baidu/boteye_sensor/hardware/XP3/schematic&PCB PDF/schematic/XPIAC-C_1V3_SCH.pdf

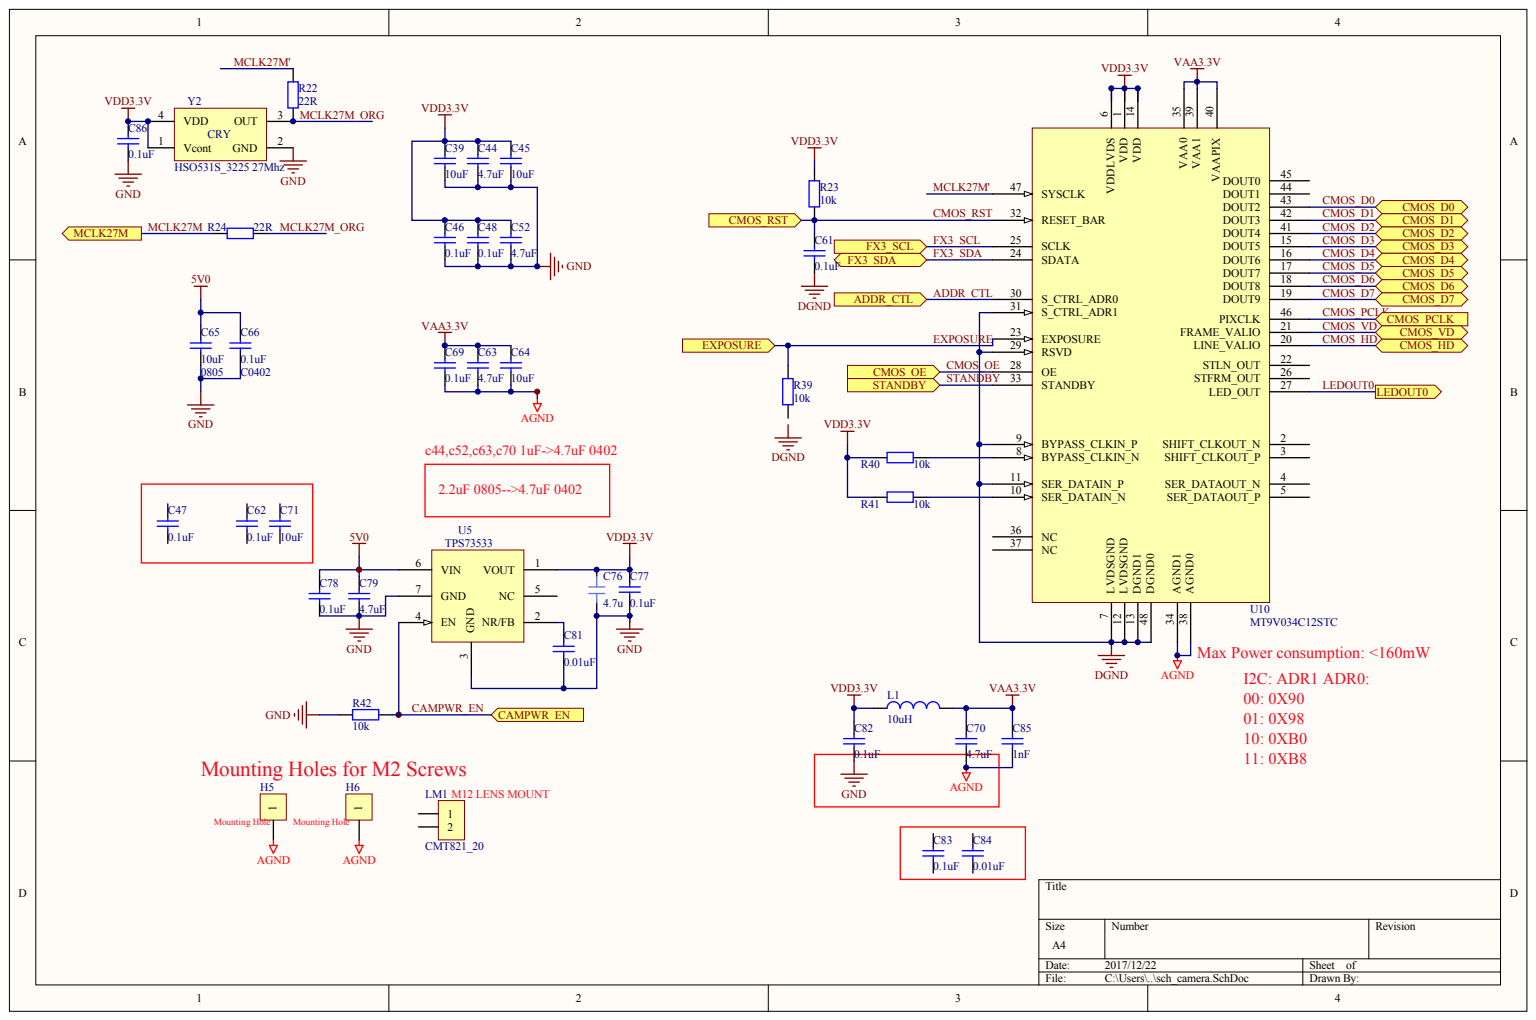
[picture p18: page 1]

Mounting Holes for M2 Screws

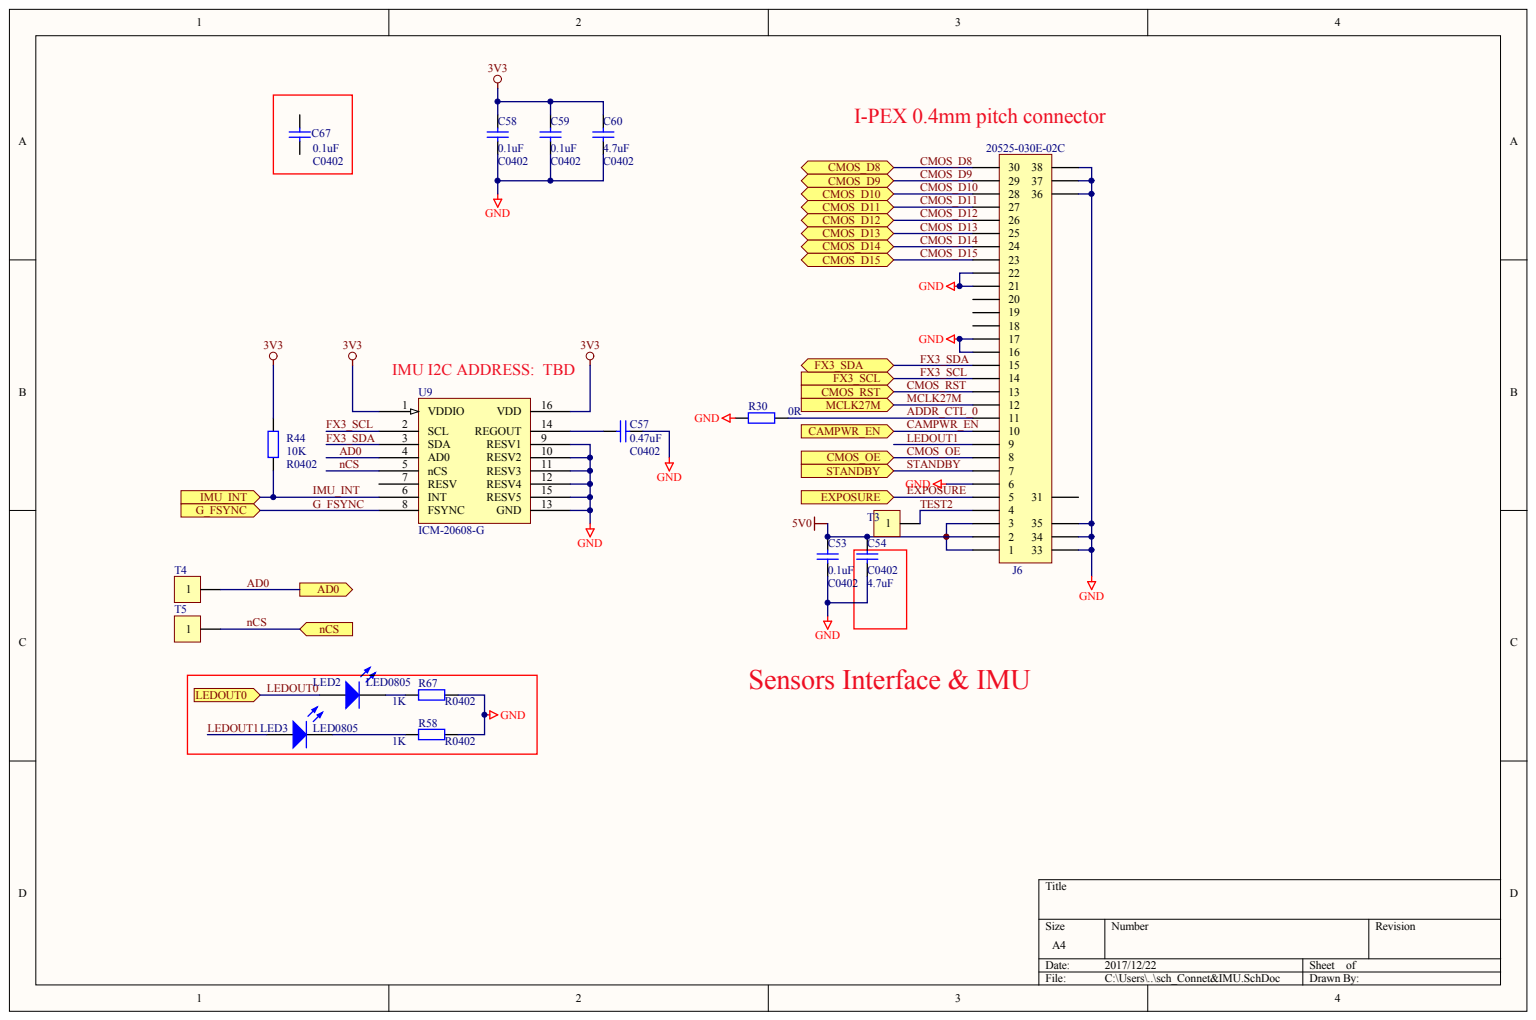
[picture p19: page 2]

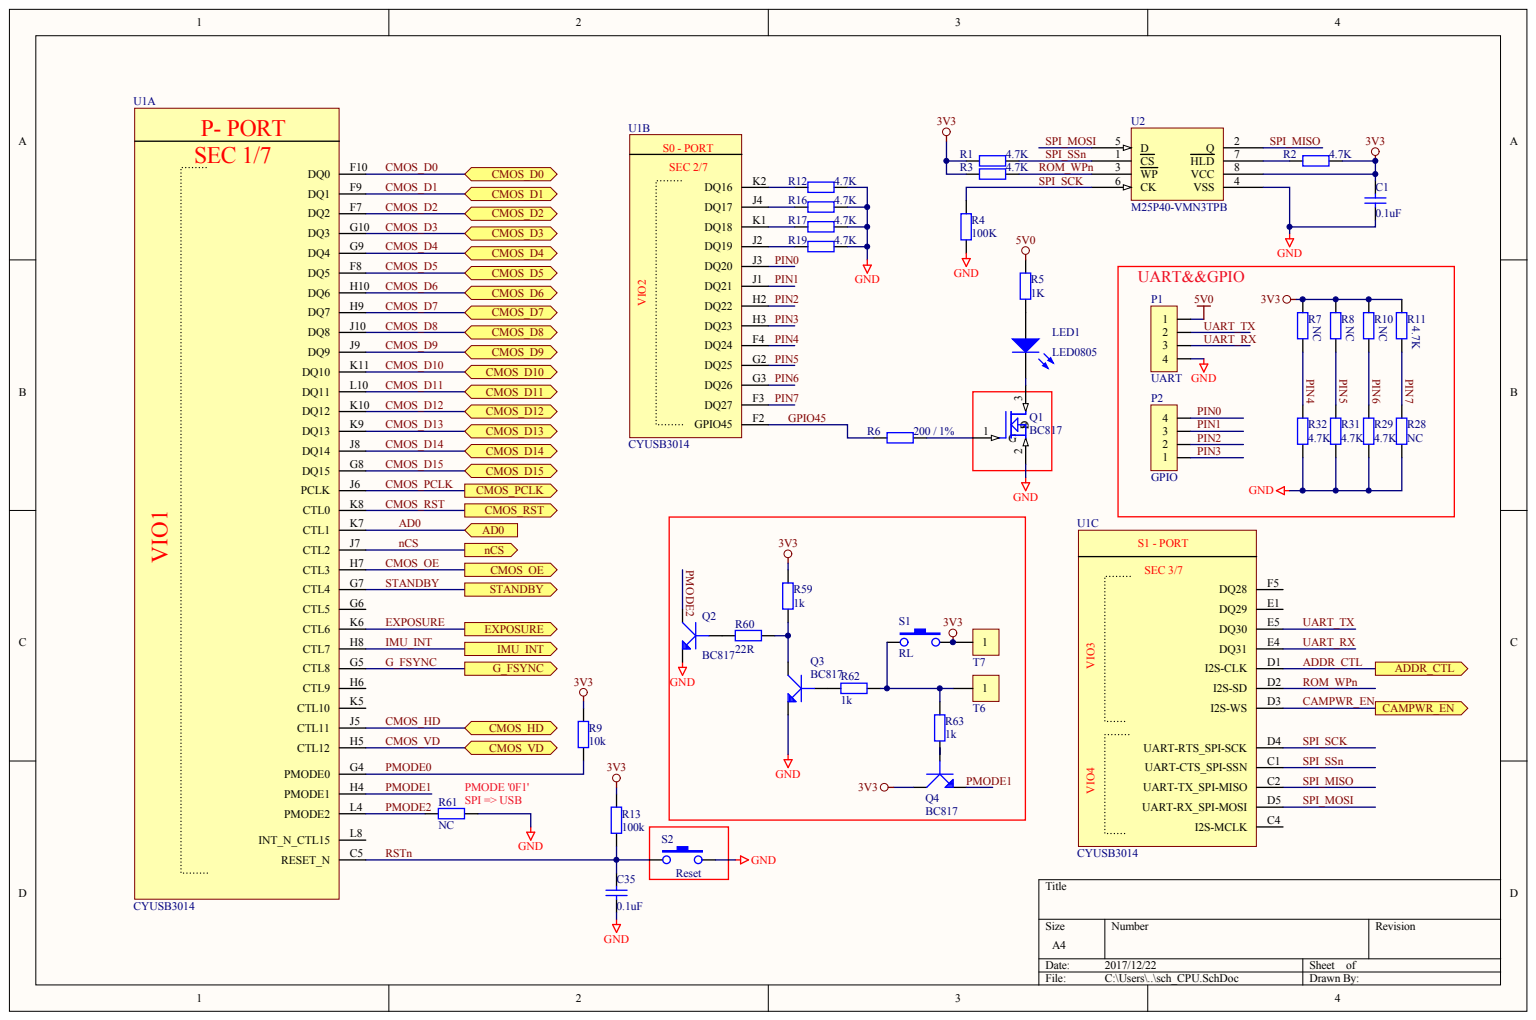
[picture p20: page 3]

SEC 2/ | 7

R3 | 4.7 K ROM _WPn 3

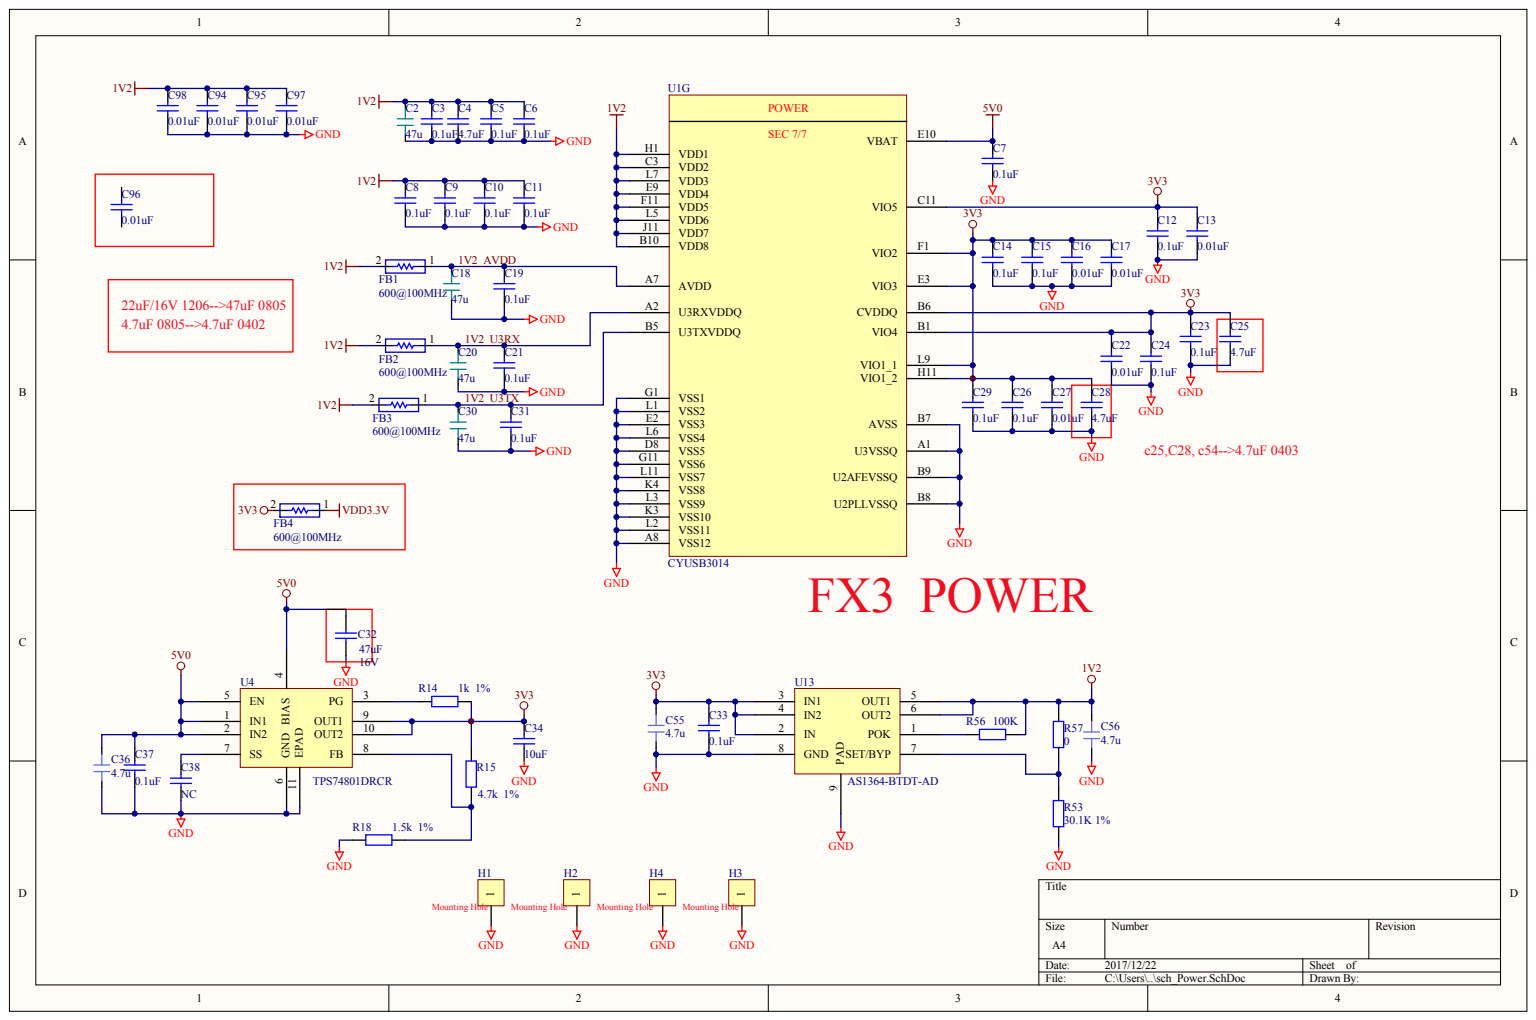
[picture p21: page 4]

VDD3 L7

VDD5 F11
VDD6 L5

U3RXVDDQ A2
U3TXVDDQ B5

VSS2 L1
VSS3 E2
VSS4 L6
VSS5 D8
VSS6 G11
VSS7 L11
VSS8 K4
VSS9 L3
VSS10 K3


CMOS_RST
CMOS_D0 EXPOSURE
CMOS_D1 STANDBY
CMOS_D2 CAMPWR_EN
CMOS_D3 IMU_INT CMOS_D4 G_FSYNC CMOS_D5 AD0 CMOS_D6 nCS CMOS_D7 ADDR_CTL

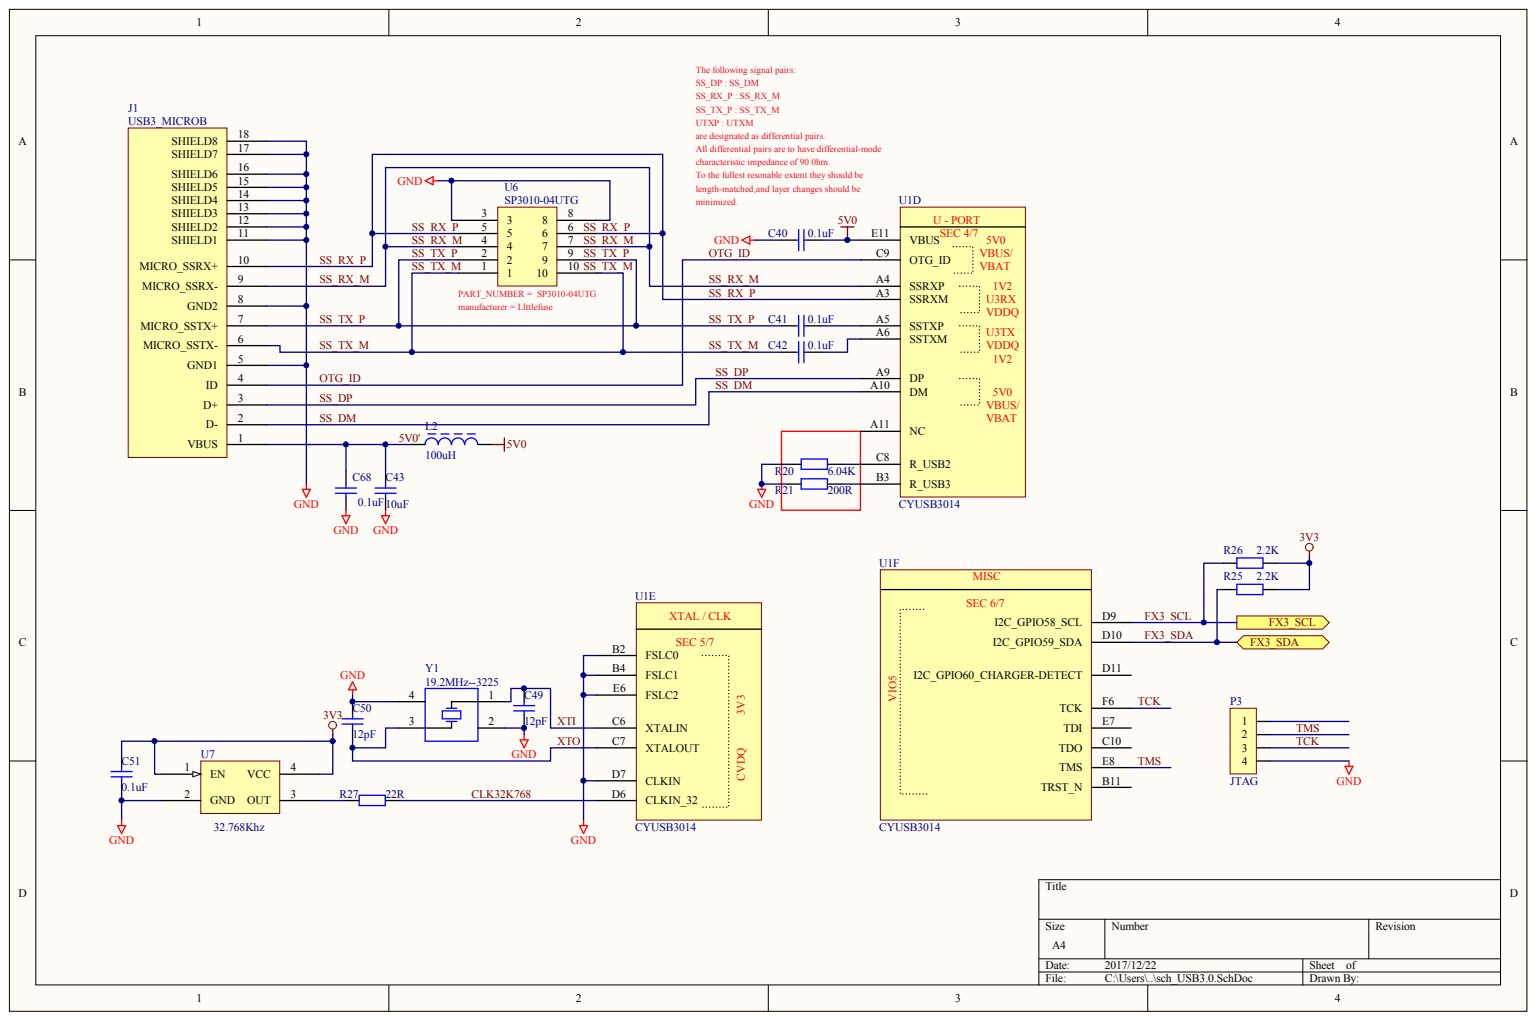
[picture p22: page 6]

The following signal pairs:
UTXP : UTXM
are designated as differential pairs.
All differential pairs are to have differential-mode
characteristic impedance of 90 0hm.
To the fullest resonable extent they should be
length-matched,and layer changes should be
minimized.

SS_RX_M | 4 4 | SS_RX_M
SS_TX_P | 1 1 2 2 | SS_TX_P
SS_TX_M | SS_TX_M | SS_RX_M | SSRXM A3 SSRXP A4

SS_DP | | NC A11
SS_DM

R_USB2 C8

R20 | 6.04K | R_USB3 B3

FSLC1 B4
FSLC2 E6

XTALIN C6

12pF | | XTALOUT C7

GND
