baidu/boteye_sensor/firmware/include/xp_sensor_firmware_version.h

#ifndef __XP_SENSOR_FIRMWARE_VERSION_H__
#define __XP_SENSOR_FIRMWARE_VERSION_H__

#define FIRMWARE_VERSION "V0.9.10-bf037c7-dirty!"

#define COMPILE_BY "yanghongtian"
#define COMPILE_HOST "xper"
#define COMPILE_TIME "15:49:25"
#define COMPILE_DATE "2018-11-19"

#endif
