baidu/boteye_sensor/firmware/cyfxuvcdscr.c

/*
 ## Cypress FX3 Camera Kit Source file (cyfxuvcdscr.c)
 ## ===========================
 ##
 ##  Copyright Cypress Semiconductor Corporation, 2010-2012,
 ##  All Rights Reserved
 ##  UNPUBLISHED, LICENSED SOFTWARE.
 ##
 ##  CONFIDENTIAL AND PROPRIETARY INFORMATION
 ##  WHICH IS THE PROPERTY OF CYPRESS.
 ##
 ##  Use of this file is governed
 ##  by the license agreement included in the file
 ##
 ##     <install>/license/license.txt
 ##
 ##  where <install> is the Cypress software
 ##  installation root directory path.
 ##
 ## ===========================
*/

/*
 * This file contains the USB descriptors for the FX3 HD 720p camera kit
 * application.
 */
#include <cyu3spi.h>
#include <cyu3error.h>
#include "include/uvc.h"
#include "include/camera_ptzcontrol.h"
#include "include/LI_USB30_SENSORs.h"
#include "include/xp_sensor_firmware_version.h"
#include "include/fx3_bsp.h"
#include "include/debug.h"
#include "include/extension_unit.h"

// Standard Device Descriptor
const uint8_t CyFxUSBDeviceDscr[] = {
    0x12,                           // Descriptor Size
    CY_U3P_USB_DEVICE_DESCR,        // Device Descriptor Type
    0x00, 0x02,                     // USB 2.0
    0xEF,                           // Device Class
    0x02,                           // Device Sub-class
    0x01,                           // Device protocol
    0x40,                           // Maxpacket size for EP0 : 64 bytes
    0xB4, 0x04,                     // Vendor ID
    0xF5, 0x00,                     // Product ID
    0x00, 0x00,                     // Device release number
    0x01,                           // Manufacture string index
    0x02,                           // Product string index
    0x03,                           // Serial number string index
    0x01                            // Number of configurations
};

// Device Descriptor for SS
const uint8_t CyFxUSBDeviceDscrSS[] = {
    0x12,                           // Descriptor Size
    CY_U3P_USB_DEVICE_DESCR,        // Device Descriptor Type
    0x00, 0x03,                     // USB 3.0
    0xEF,                           // Device Class
    0x02,                           // Device Sub-class
    0x01,                           // Device protocol
    0x09,                           // Maxpacket size for EP0 : 2^9 Bytes
    0xB4, 0x04,                     // Vendor ID
    0xF5, 0x00,                     // Product ID
    0x00, 0x00,                     // Device release number
    0x01,                           // Manufacture string index
    0x02,                           // Product string index
    0x03,                           // Serial number string index
    0x01                            // Number of configurations
};

// Standard Device Qualifier Descriptor
const uint8_t CyFxUSBDeviceQualDscr[] = {
    0x0A,                           // Descriptor Size
    CY_U3P_USB_DEVQUAL_DESCR,       // Device Qualifier Descriptor Type
    0x00, 0x02,                     // USB 2.0
    0xEF,                           // Device Class
    0x02,                           // Device Sub-class
    0x01,                           // Device protocol
    0x40,                           // Maxpacket size for EP0 : 64 bytes
    0x01,                           // Number of configurations
    0x00                            // Reserved
};

// Standard Full Speed Configuration Descriptor
const uint8_t CyFxUSBFSConfigDscr[] = {
    // Configuration Descriptor Type
    0x09,                           // Descriptor Size
    CY_U3P_USB_CONFIG_DESCR,        // Configuration Descriptor Type
    0x09, 0x00,                     // Length of this descriptor and all sub descriptors
    0x00,                           // Number of interfaces
    0x01,                           // Configuration number
    0x00,                           // COnfiguration string index
    0x80,                           // Config characteristics - Bus powered
    0x32,                           // Max power consumption of device (in 2mA unit) : 100mA
};

// Standard High Speed Configuration Descriptor
uint8_t CyFxUSBHSConfigDscr[] = {
    // Configuration Descriptor Type
    0x09,                           // Descriptor Size
    CY_U3P_USB_CONFIG_DESCR,        // Configuration Descriptor Type
    0xCD, 0x00,                     // Length of this descriptor and all sub descriptors
    0x02,                           // Number of interfaces
    0x01,                           // Configuration number
    0x00,                           // COnfiguration string index
    0x80,                           // Config characteristics - Bus powered
    0xFA,                           // Max power consumption of device (in 2mA unit) : 500mA

    // Interface Association Descriptor
    0x08,                           // Descriptor Size
    CY_FX_INTF_ASSN_DSCR_TYPE,      // Interface Association Descr Type: 11
    0x00,                           // I/f number of first VideoControl i/f
    0x02,                           // Number of Video i/f
    0x0E,                           // CC_VIDEO : Video i/f class code
    0x03,                           // SC_VIDEO_INTERFACE_COLLECTION : Subclass code
    0x00,                           // Protocol : Not used
    0x00,                           // String desc index for interface

    // Standard Video Control Interface Descriptor
    0x09,                           // Descriptor size
    CY_U3P_USB_INTRFC_DESCR,        // Interface Descriptor type
    0x00,                           // Interface number
    0x00,                           // Alternate setting number
    0x01,                           // Number of end points
    0x0E,                           // CC_VIDEO : Interface class
    0x01,                           // CC_VIDEOCONTROL : Interface sub class
    0x00,                           // Interface protocol code
    0x00,                           // Interface descriptor string index

    // Class specific VC Interface Header Descriptor
    0x0D,                           // Descriptor size
    0x24,                           // Class Specific I/f Header Descriptor type
    0x01,                           // Descriptor Sub type : VC_HEADER
    0x00, 0x01,                     // Revision of class spec : 1.0
    0x50, 0x00,                     // Total Size of class specific descriptors
    0x00, 0x6C, 0xDC, 0x02,         // Clock frequency : 48MHz(Deprecated)
    0x01,                           // Number of streaming interfaces
    0x01,                           // Video streaming I/f 1 belongs to VC i/f

    // Input (Camera) Terminal Descriptor
    0x12,                           // Descriptor size
    0x24,                           // Class specific interface desc type
    0x02,                           // Input Terminal Descriptor type
    0x01,                           // ID of this terminal
    0x01, 0x02,                     // Camera terminal type
    0x00,                           // No association terminal
    0x00,                           // String desc index : Not used
#ifdef UVC_PTZ_SUPPORT
    (uint8_t)(wObjectiveFocalLengthMin&0xFF),
    (uint8_t)((wObjectiveFocalLengthMin>>8)&0xFF),
    (uint8_t)(wObjectiveFocalLengthMax&0xFF),
    (uint8_t)((wObjectiveFocalLengthMax>>8)&0xFF),
    (uint8_t)(wOcularFocalLength&0xFF),
    (uint8_t)((wOcularFocalLength>>8)&0xFF),
#else
    0x00, 0x00,                     // No optical zoom supported
    0x00, 0x00,                     // No optical zoom supported
    0x00, 0x00,                     // No optical zoom supported
#endif
    0x03,                           // Size of controls field for this terminal : 3 bytes
#ifdef UVC_PTZ_SUPPORT
    0x08, 0x0A, 0x00,
#else
    0x08, 0x00, 0x00,
#endif

    // Processing Unit Descriptor
    0x0C,                           // Descriptor size
    0x24,                           // Class specific interface desc type
    0x05,                           // Processing Unit Descriptor type
    0x02,                           // ID of this terminal
    0x01,                           // Source ID : 1 : Conencted to input terminal
    0x00, 0x40,                     // Digital multiplier
    0x03,                           // Size of controls field for this terminal : 3 bytes
    0x01, 0x02, 0x00,               // No controls supported
    0x00,                           // String desc index : Not used

    // Extension Unit Descriptor
    0x1C,                           // Descriptor size
    0x24,                           // Class specific interface desc type
    0x06,                           // Extension Unit Descriptor type
    0x03,                           // ID of this terminal
    0xFF, 0xFF, 0xFF, 0xFF,         // 16 byte GUID
    0xFF, 0xFF, 0xFF, 0xFF,
    0xFF, 0xFF, 0xFF, 0xFF,
    0xFF, 0xFF, 0xFF, 0xFF,
    0x03,                           // Number of controls in this terminal
    0x01,                           // Number of input pins in this terminal
    0x02,                           // Source ID : 2 : Connected to Proc Unit
    0x03,                           // Size of controls field for this terminal : 3 bytes
    0xFF, 0xFF, 0xFF,
    0x00,                           // String desc index : Not used

    // Output Terminal Descriptor
    0x09,                           // Descriptor size
    0x24,                           // Class specific interface desc type
    0x03,                           // Output Terminal Descriptor type
    0x04,                           // ID of this terminal
    0x01, 0x01,                     // USB Streaming terminal type
    0x00,                           // No association terminal
    0x03,                           // Source ID : 3 : Connected to Extn Unit
    0x00,                           // String desc index : Not used

    // Video Control Status Interrupt Endpoint Descriptor
    0x07,                           // Descriptor size
    CY_U3P_USB_ENDPNT_DESCR,        // Endpoint Descriptor Type
    CY_FX_EP_CONTROL_STATUS,        // Endpoint address and description
    CY_U3P_USB_EP_INTR,             // Interrupt End point Type
    0x40, 0x00,                     // Max packet size = 64 bytes
    0x08,                           // Servicing interval : 8ms

    // Class Specific Interrupt Endpoint Descriptor
    0x05,                           // Descriptor size
    0x25,                           // Class Specific Endpoint Descriptor Type
    CY_U3P_USB_EP_INTR,             // End point Sub Type
    0x40, 0x00,                     // Max packet size = 64 bytes

    // Standard Video Streaming Interface Descriptor (Alternate Setting 0)
    0x09,                           // Descriptor size
    CY_U3P_USB_INTRFC_DESCR,        // Interface Descriptor type
    0x01,                           // Interface number
    0x00,                           // Alternate setting number
    0x01,                           // Number of end points : Zero Bandwidth
    0x0E,                           // Interface class : CC_VIDEO
    0x02,                           // Interface sub class : CC_VIDEOSTREAMING
    0x00,                           // Interface protocol code : Undefined
    0x00,                           // Interface descriptor string index

    // Class-specific Video Streaming Input Header Descriptor
    0x0E,                           // Descriptor size
    0x24,                           // Class-specific VS I/f Type
    0x01,                           // Descriptotor Subtype : Input Header
    0x01,                           // 1 format desciptor follows
    0x29, 0x00,                     // Total size of Class specific VS descr: 41 Bytes
    CY_FX_EP_BULK_VIDEO,            // EP address for BULK video data
    0x00,                           // No dynamic format change supported
    0x04,                           // Output terminal ID : 4
    0x01,                           // Still image capture method 1 supported
    0x00,                           // Hardware trigger NOT supported
    0x00,                           // Hardware to initiate still image capture NOT supported
    0x01,                           // Size of controls field : 1 byte
    0x00,                           // D2 : Compression quality supported


    // Class specific Uncompressed VS format descriptor
    0x1B,                           // Descriptor size
    0x24,                           // Class-specific VS I/f Type
    0x04,                           // Subtype : uncompressed format I/F
    0x01,                           // Format desciptor index (only one format is supported)
    0x01,                           // number of frame descriptor followed
    0x59, 0x55, 0x59, 0x32,         // GUID used to identify streaming-encoding format: YUY2
    0x00, 0x00, 0x10, 0x00,
    0x80, 0x00, 0x00, 0xAA,
    0x00, 0x38, 0x9B, 0x71,
    0x10,                           // Number of bits per pixel used to specify color in the decoded
                                    // video frame.0 if not applicable: 10 bit per pixel
    0x01,                           // Optimum Frame Index for this stream: 1
    0x08,                           // X dimension of the picture aspect ratio: Non-interlaced in
                                    // progressive scan
    0x06,                           // Y dimension of the picture aspect ratio: Non-interlaced in
                                    // progressive scan
    0x00,                           // Interlace Flags: Progressive scanning, no interlace
    0x00,                           // duplication of video stream restriction: 0- no restriction

    // Class specific Uncompressed VS Frame descriptor
    0x1E,                           // Descriptor size
    0x24,                           // Descriptor type*/
    0x05,                           // Subtype: uncompressed frame I/F
    0x01,                           // Frame Descriptor Index
    0x03,                           // Still image capture method 1 supported, fixed frame rate
    0x80, 0x02,                     // Width in pixel: 640-VGA
    0xE0, 0x01,                     // Height in pixel 480-VGA
    0x00, 0x50, 0x97, 0x31,         // Min bit rate bits/s. Not specified, taken from MJPEG
    0x00, 0x50, 0x97, 0x31,         // Max bit rate bits/s. Not specified, taken from MJPEG
    0x00, 0x60, 0x09, 0x00,         // Maximum video or still frame size in bytes(Deprecated)
    0x2A, 0x2C, 0x0A, 0x00,         // Default Frame Interval
    0x01,                           // Frame interval(Frame Rate) types: Only one frame interval
                                    // supported
    0x2A, 0x2C, 0x0A, 0x00,         // Shortest Frame Interval

    // Endpoint Descriptor for BULK Streaming Video Data
    0x07,                           // Descriptor size
    CY_U3P_USB_ENDPNT_DESCR,        // Endpoint Descriptor Type
    CY_FX_EP_BULK_VIDEO,            // Endpoint address and description
    0x02,                           // BULK End point
    (uint8_t)(512 & 0x00FF),        // High speed max packet size is always 512 bytes.
    (uint8_t)((512 & 0xFF00)>>8),
    0x01                            // Servicing interval for data transfers
};

// BOS for SS

#define CY_FX_BOS_DSCR_TYPE             15
#define CY_FX_DEVICE_CAPB_DSCR_TYPE     16
#define CY_FX_SS_EP_COMPN_DSCR_TYPE     48

// Device Capability Type Codes
#define CY_FX_WIRELESS_USB_CAPB_TYPE    1
#define CY_FX_USB2_EXTN_CAPB_TYPE       2
#define CY_FX_SS_USB_CAPB_TYPE          3
#define CY_FX_CONTAINER_ID_CAPBD_TYPE   4

const uint8_t CyFxUSBBOSDscr[] = {
    0x05,                           // Descriptor Size
    CY_FX_BOS_DSCR_TYPE,            // Device Descriptor Type
    0x16, 0x00,                     // Length of this descriptor and all sub descriptors
    0x02,                           // Number of device capability descriptors

    // USB 2.0 Extension
    0x07,                           // Descriptor Size
    CY_FX_DEVICE_CAPB_DSCR_TYPE,    // Device Capability Type descriptor
    CY_FX_USB2_EXTN_CAPB_TYPE,      // USB 2.0 Extension Capability Type
    // 0x00, 0x00, 0x00, 0x00,      // Supported device level features
    0x02, 0x00, 0x00, 0x00,         // CHANGE to support LPM, Supported device level features

    // SuperSpeed Device Capability
    0x0A,                           // Descriptor Size
    CY_FX_DEVICE_CAPB_DSCR_TYPE,    // Device Capability Type descriptor
    CY_FX_SS_USB_CAPB_TYPE,         // SuperSpeed Device Capability Type
    0x00,                           // Supported device level features
    0x0E, 0x00,                     // Speeds Supported by the device : SS, HS and FS
    0x03,                           // Functionality support
    0x00,                           // U1 Device Exit Latency
    0x00, 0x00                      // U2 Device Exit Latency
};

// Super Speed Configuration Descriptor
uint8_t CyFxUSBSSConfigDscr[] = {
    // Configuration Descriptor Type
    0x09,                           // Descriptor Size
    CY_U3P_USB_CONFIG_DESCR,        // Configuration Descriptor Type
    // 0x57, 0x01,
    0xE4, 0x00,
    0x02,
    0x01,                           // Configuration number
    0x00,                           // Configuration string index
    0x80,                           // Config characteristics - Bus powered
    0x32,                           // Max power consumption of device (in 8mA unit) : 400mA

    // Interface Association Descriptor
    0x08,                           // Descriptor Size
    CY_FX_INTF_ASSN_DSCR_TYPE,      // Interface Association Descr Type: 11
    0x00,                           // I/f number of first VideoControl i/f
    0x02,                           // Number of Video i/f
    0x0E,                           // CC_VIDEO : Video i/f class code
    0x03,                           // SC_VIDEO_INTERFACE_COLLECTION : Subclass code
    0x00,                           // Protocol : Not used
    0x00,                           // String desc index for interface

    // Standard Video Control Interface Descriptor
    0x09,                           // Descriptor size
    CY_U3P_USB_INTRFC_DESCR,        // Interface Descriptor type
    0x00,                           // Interface number
    0x00,                           // Alternate setting number
    0x01,                           // Number of end points
    0x0E,                           // CC_VIDEO : Interface class
    0x01,                           // CC_VIDEOCONTROL : Interface sub class
    0x00,                           // Interface protocol code
    0x00,                           // Interface descriptor string index

    // Class specific VC Interface Header Descriptor
    0x0D,                           // Descriptor size
    0x24,                           // Class Specific I/f Header Descriptor type
    0x01,                           // Descriptor Sub type : VC_HEADER
    0x00, 0x01,                     // org,0x00,0x10,kg USB30CV, CAN NOT be changed,ERROR FX3,
                                    // Revision of class spec : 1.0
    0x4F, 0x00,
    0x00, 0x6C, 0xDC, 0x02,         // Clock frequency : 48MHz(Deprecated)
    0x01,                           // Number of streaming interfaces
    0x01,                           // Video streaming I/f 1 belongs to VC i/f

    // Input (Camera) Terminal Descriptor
    0x12,                           // Descriptor size
    0x24,                           // Class specific interface desc type
    0x02,                           // Input Terminal Descriptor type
    0x01,                           // ID of this terminal
    0x01, 0x02,                     // Camera terminal type
    0x04,                           // kg, org 0x00 No association terminal
    0x00,                           // String desc index : Not used
#ifdef UVC_PTZ_SUPPORT
    (uint8_t)(wObjectiveFocalLengthMin&0xFF),
    (uint8_t)((wObjectiveFocalLengthMin>>8)&0xFF),
    (uint8_t)(wObjectiveFocalLengthMax&0xFF),
    (uint8_t)((wObjectiveFocalLengthMax>>8)&0xFF),
    (uint8_t)(wOcularFocalLength&0xFF),
    (uint8_t)((wOcularFocalLength>>8)&0xFF),
#else
    0x00, 0x00,                     // No optical zoom supported
    0x00, 0x00,                     // No optical zoom supported
    0x00, 0x00,                     // No optical zoom supported
#endif
    0x03,                           // Size of controls field for this terminal : 3 bytes
#ifdef UVC_PTZ_SUPPORT
    0x08, 0x0A, 0x00,
#else
    0x08, 0x00, 0x00,               // We have exposure control*/
#endif

    // Processing Unit Descriptor
    0x0B,                           // Descriptor size
    0x24,                           // Class specific interface desc type
    0x05,                           // Processing Unit Descriptor type
    0x02,                           // ID of this terminal
    0x01,                           // Source ID : 1 : Conencted to input terminal
    0x00, 0x40,                     // Digital multiplier
    0x02,                           // Size of controls field for this terminal : 3 bytes
    0x01, 0x02,                     // UVC control
    0x00,                           // String desc index : Not used

    // Extension Unit Descriptor
    0x1C,                           // Descriptor size
    0x24,                           // Class specific interface desc type
    0x06,                           // Extension Unit Descriptor type
    0x03,                           // ID of this terminal
    0xFF, 0xFF, 0xFF, 0xFF,         // 16 byte GUID
    0xFF, 0xFF, 0xFF, 0xFF,
    0xFF, 0xFF, 0xFF, 0xFF,
    0xFF, 0xFF, 0xFF, 0xFF,
    0x03,                           // Number of controls in this terminal
    0x01,                           // Number of input pins in this terminal
    0x02,                           // Source ID : 2 : Connected to Proc Unit
    0x03,                           // Size of controls field for this terminal : 3 bytes
    0xFF, 0xFF, 0xFF,               // No controls supported
    0x00,                           // String desc index : Not used

    // Output Terminal Descriptor
    0x09,                           // Descriptor size
    0x24,                           // Class specific interface desc type
    0x03,                           // Output Terminal Descriptor type
    0x04,                           // ID of this terminal
    0x01, 0x01,                     // USB Streaming terminal type
    0x00,                           // No association terminal
    0x03,                           // Source ID : 3 : Connected to Extn Unit
    0x00,                           // String desc index : Not used

    // Video Control Status Interrupt Endpoint Descriptor
    0x07,                           // Descriptor size
    CY_U3P_USB_ENDPNT_DESCR,        // Endpoint Descriptor Type
    CY_FX_EP_CONTROL_STATUS,        // Endpoint address and description
    CY_U3P_USB_EP_INTR,             // Interrupt End point Type
    // 0x00,0x04,                   // Max packet size = 1024 bytes
    0x40, 0x00,                     // Change to 64, based on USB30CV
    0x01,                           // Servicing interval

    // Super Speed Endpoint Companion Descriptor
    0x06,                           // Descriptor size
    CY_U3P_SS_EP_COMPN_DESCR,       // SS Endpoint Companion Descriptor Type
    0x00,                           // Max no. of packets in a Burst : 1
    0x00,                           // Attribute: N.A.
    0x00,                           // Bytes per interval:1024
    0x04,

    // Class Specific Interrupt Endpoint Descriptor
    0x05,                           // Descriptor size
    0x25,                           // Class Specific Endpoint Descriptor Type
    CY_U3P_USB_EP_INTR,             // End point Sub Type
    0x40, 0x00,                      // Max packet size = 64 bytes


    // Standard Video Streaming Interface Descriptor (Alternate Setting 0)
    0x09,                           // Descriptor size
    CY_U3P_USB_INTRFC_DESCR,        // Interface Descriptor type
    0x01,                           // Interface number
    0x00,                           // Alternate setting number
    0x01,                           // Number of end points
    0x0E,                           // Interface class : CC_VIDEO
    0x02,                           // Interface sub class : CC_VIDEOSTREAMING
    0x00,                           // Interface protocol code : Undefined
    0x00,                           // Interface descriptor string index

    // Class-specific Video Streaming Input Header Descriptor
    0x0E,                           // Descriptor size
    0x24,                           // Class-specific VS I/f Type
    0x01,                           // Descriptotor Subtype : Input Header
    0x01,                           // 1 format desciptor follows  support more resolutions*/
    0x53, 0x00,
    CY_FX_EP_BULK_VIDEO,            // EP address for BULK video data
    0x00,                           // No dynamic format change supported
    0x04,                           // Output terminal ID : 4
    0x01,                           // Still image capture method 1 supported
    0x00,                           // Hardware trigger NOT supported
    0x00,                           // Hardware to initiate still image capture NOT supported
    0x01,                           // Size of controls field : 1 byte
    0x00,                           // D2 : Compression quality supported

    // Class specific Uncompressed VS format descriptor
    0x1B,                           // Descriptor size
    0x24,                           // Class-specific VS I/f Type
    0x04,                           // Subtype : uncompressed format I/F
    0x01,                           // Format desciptor index
    RES_NUM,                        // Number of frame descriptor followed
    0x59, 0x55, 0x59, 0x32,         // GUID used to identify streaming-encoding format: YUY2
    0x00, 0x00, 0x10, 0x00,
    0x80, 0x00, 0x00, 0xAA,
    0x00, 0x38, 0x9B, 0x71,
    0x10,                           // Number of bits per pixel
    0x01,                           // Optimum Frame Index for this stream: 1
    0x10,                           // X dimension of the picture aspect ratio; Non-interlaced
    0x09,                           // Y dimension of the pictuer aspect ratio: Non-interlaced
    0x00,                           // Interlace Flags: Progressive scanning, no interlace
    0x00,                           // duplication of video stream restriction: 0- no restriction

    // Class specific Uncompressed VS frame descriptor
    // CS_UNCOMPRESSED_VS_FRAME_DESCRIPTOR_LENGTH,  // Descriptor size
    0x2a,                           // Descriptor size
    0x24,                           // Descriptor type*/
    0x05,                           // Subtype: uncompressed frame I/F
    0x01,                           // Frame Descriptor Index
    0x01,  // org,0x03,kg,USB30CV   // Still image capture method 1 supported, fixed frame rate
    0x80, 0x02,                     // Width in pixel
    0xE0, 0x01,                     // 640*480,4:3,but not right,Height in pixel
    0x00, 0x50, 0x97, 0x31,         // Min bit rate bits/s.
    0x00, 0x50, 0x97, 0x31,         // Max bit rate bits/s.
    0x00, 0xA4, 0x1F, 0x00,         // Maximum video or still frame size in bytes(Deprecated)
    0x0A, 0x8B, 0x02, 0x00,         // current vaule: 30fps if want 60fps: 0x15,0x16,0x05,0x00
    SUPPORTED_FRAMERATE_NUM,
    0x0A, 0x8B, 0x02, 0x00,         // 60fps
    0x15, 0x16, 0x05, 0x00,
    0x2A, 0x2C, 0x0A, 0x00,         // Maximum Frame interval
    0x40, 0x42, 0x0F, 0x00,         // Frame interval STEP

    // Endpoint Descriptor for BULK Streaming Video Data
    0x07,                           // Descriptor size
    CY_U3P_USB_ENDPNT_DESCR,        // Endpoint Descriptor Type
    CY_FX_EP_BULK_VIDEO,            // Endpoint address and description
    CY_U3P_USB_EP_BULK,             // BULK End point
    CY_FX_EP_BULK_VIDEO_PKT_SIZE_L,  // EP MaxPcktSize: 1024B
    CY_FX_EP_BULK_VIDEO_PKT_SIZE_H,  // EP MaxPcktSize: 1024B
    // 0x01,                        // Servicing interval for data transfers
    0x00,                           // CHANGE to 0x00,based on USB30CV

    // Super Speed Endpoint Companion Descriptor
    0x06,                           // Descriptor size
    CY_U3P_SS_EP_COMPN_DESCR,       // SS Endpoint Companion Descriptor Type
    0x0F,                           // Max number of packets per burst: 16
    0x00,                           // Attribute: Streams not defined
    0x00,                           // No meaning for bulk
    0x00
};

// Standard Language ID String Descriptor
const uint8_t CyFxUSBStringLangIDDscr[] = {
    0x04,                           // Descriptor Size
    CY_U3P_USB_STRING_DESCR,        // Device Descriptor Type
    0x09, 0x04                      // Language ID supported
};

// Standard Manufacturer String Descriptor
const uint8_t CyFxUSBManufactureDscr[] = {
    0x0C,                           // Descriptor Size
    CY_U3P_USB_STRING_DESCR,        // Device Descriptor Type
    'B', 0x00,
    'a', 0x00,
    'i', 0x00,
    'd', 0x00,
    'u', 0x00
};


// Standard Product String Descriptor
uint8_t CyFxUSBProductDscr[256] = {
    0x14,                           // Descriptor Size
    CY_U3P_USB_STRING_DESCR,        // Device Descriptor Type
    'B', 0x00,
    'a', 0x00,
    'i', 0x00,
    'd', 0x00,
    'u', 0x00,
    'C', 0x00,
    'a', 0x00,
    'm', 0x00,
    '2', 0x00
};

uint8_t CyFxUSBSerialNumberDscr[256] = {
    0x1A,                           // Descriptor Size
    CY_U3P_USB_STRING_DESCR,        // Device Descriptor Type
    'V', 0x00,
    '0', 0x00,
    '3', 0x00,
    '4', 0x00,
    '0', 0x00,
    '0', 0x00,
    '0', 0x00,
    '0', 0x00,
    '0', 0x00,
    '0', 0x00,
    '0', 0x00,
    '1', 0x00
};

/**
 *  @brief      update firmware vesion and device ID to Serial Number Descriptor.
 *  @param[out] NULL.
 *  @return     NULL.
 */
void update_serial_number_dscr(void) {
  int i = 0;
  char *version_info = FIRMWARE_VERSION;
  const char *error_info = "device ID NULL or too long";
  int version_len = strlen(version_info);
  struct flash_struct_t flash_store;
  uint16_t flash_len = sizeof (struct flash_struct_t);
  CyU3PReturnStatus_t apiRetStatus = CY_U3P_SUCCESS;

  CyU3PMemSet((uint8_t *)(&flash_store), 0, flash_len);
  apiRetStatus = CyFxFlashProgSpiTransfer(DEVICE_MSG_ADDR, flash_len, (uint8_t *)(&flash_store),
                                            CyTrue);
  if (apiRetStatus != CY_U3P_SUCCESS) {
    sensor_err("read Flash error\r\n");
  }
  uint16_t deviceID_len = strlen((char *)(&(flash_store.Sensor_ID)));
  memset(CyFxUSBSerialNumberDscr, 0, sizeof(CyFxUSBSerialNumberDscr));
  CyFxUSBSerialNumberDscr[1] = CY_U3P_USB_STRING_DESCR;

  for (i = 0; i < version_len; i++) {
    CyFxUSBSerialNumberDscr[2 + i * 2] = *(version_info + i);
  }
  CyFxUSBSerialNumberDscr[2 + version_len * 2] = '-';
  if ((version_len + deviceID_len + 1) <= (256 - 2) >> 2) {
    CyFxUSBSerialNumberDscr[0] = 2 + (version_len + deviceID_len + 1) * 2;
    for (i = 0; i < deviceID_len; i++) {
      CyFxUSBSerialNumberDscr[2 + version_len * 2 + 2 + i * 2] = flash_store.Sensor_ID[i];
    }
  } else {
    CyFxUSBSerialNumberDscr[0] = 2 + (version_len + strlen(error_info) + 1) * 2;
    CyFxUSBSerialNumberDscr[1] = CY_U3P_USB_STRING_DESCR;
    for (i = 0; i < strlen(error_info); i++) {
      CyFxUSBSerialNumberDscr[2 + version_len * 2 + 2 + i * 2] = *(error_info + i);
    }
  }
}

/**
 *  @brief      update hardware vesion to Product String Descriptor.
 *  @param[out] NULL.
 *  @return     NULL.
 */
void update_hard_version_dscr(void) {
  int i = 0;
  char *hard_version_info = Baidu_ProductDscr[hardware_version_num];
  sensor_info("hard_version_info:%s\r\n", hard_version_info);
  int version_len = strlen(hard_version_info);

  if (version_len > (256 - 2) >> 2)
    version_len = (256 - 2) >> 2;

  memset(CyFxUSBProductDscr, 0, sizeof(CyFxUSBProductDscr));
  CyFxUSBProductDscr[0] = 2 + version_len * 2;
  CyFxUSBProductDscr[1] = CY_U3P_USB_STRING_DESCR;

  for (i = 0; i < version_len; i++) {
    CyFxUSBProductDscr[2 + i * 2] = *(hard_version_info + i);
  }
}
/**
 *  @brief      update sensor Resolution to usb2.0 Configuration Descriptor.
 *  @param[out] NULL.
 *  @return     NULL.
 */
void update_HS_config_dscr(enum SensorType sensor_type) {
  uint16_t width = 0;
  uint16_t height = 0;
  if (sensor_type == XPIRL2 || sensor_type == XPIRL3 || sensor_type == XPIRL3_A) {
    width = 1280;
    height = 720;
  } else {
    width = 640;
    height = 480;
  }
  CyFxUSBHSConfigDscr[173] = width & 0xFF;
  CyFxUSBHSConfigDscr[174] = width >> 8;
  CyFxUSBHSConfigDscr[175] = height & 0xFF;
  CyFxUSBHSConfigDscr[176] = height >> 8;
  sensor_dbg("HS config width: %d height: %d \r\n",
             CyFxUSBHSConfigDscr[173] | CyFxUSBHSConfigDscr[174] << 8,
             CyFxUSBHSConfigDscr[175] | CyFxUSBHSConfigDscr[176] << 8);
}
/**
 *  @brief      update sensor Resolution to usb3.0 Configuration Descriptor.
 *  @param[out] NULL.
 *  @return     NULL.
 */
void update_SS_config_dscr(enum SensorType sensor_type) {
  uint16_t width = 0;
  uint16_t height = 0;
  if (sensor_type == XPIRL2 || sensor_type == XPIRL3 || sensor_type == XPIRL3_A) {
    width = 1280;
    height = 720;
  } else {
    width = 640;
    height = 480;
  }
  CyFxUSBSSConfigDscr[178] = width & 0xFF;
  CyFxUSBSSConfigDscr[179] = width >> 8;
  CyFxUSBSSConfigDscr[180] = height & 0xFF;
  CyFxUSBSSConfigDscr[181] = height >> 8;
  sensor_dbg("SS config width: %d height: %d \r\n",
             CyFxUSBSSConfigDscr[178] | CyFxUSBSSConfigDscr[179] << 8,
             CyFxUSBSSConfigDscr[180] | CyFxUSBSSConfigDscr[181] << 8);
}
