baidu/boteye_sensor/firmware/include/uvc.h

/*
 ## Cypress FX3 Camera Kit header file (uvc.h)
 ## ===========================
 ##
 ##  Copyright Cypress Semiconductor Corporation, 2010-2012,
 ##  All Rights Reserved
 ##  UNPUBLISHED, LICENSED SOFTWARE.
 ##
 ##  CONFIDENTIAL AND PROPRIETARY INFORMATION
 ##  WHICH IS THE PROPERTY OF CYPRESS.
 ##
 ##  Use of this file is governed
 ##  by the license agreement included in the file
 ##
 ##     <install>/license/license.txt
 ##
 ##  where <install> is the Cypress software
 ##  installation root directory path.
 ##
 ## ===========================
*/

/* This header file defines the UVC application constants and the Video Frame configurations */

#ifndef FIRMWARE_INCLUDE_UVC_H_
#define FIRMWARE_INCLUDE_UVC_H_

#include <cyu3types.h>
#include <cyu3usbconst.h>
#include <cyu3externcstart.h>
#include <cyu3externcend.h>
#include <cyu3system.h>
#include <cyu3os.h>
#include <cyu3dma.h>
#include <cyu3error.h>
#include <cyu3usb.h>
#include <cyu3uart.h>
#include <cyu3gpif.h>
#include <cyu3i2c.h>
#include <cyu3gpio.h>
#include <cyu3pib.h>
#include <cyu3utils.h>

struct firmware_ctl_t {
    uint8_t log_dbg: 1;
    uint8_t log_info: 1;
    uint8_t log_dump: 1;
    uint8_t imu_from_image: 1;
    uint8_t print_frame_rate: 1;
    uint8_t tmp_bit: 3;
    uint8_t tmp8;
    uint16_t tmp16;
};

enum  SensorType {
  XP_XP2 = 0,
  XP2s = 1,
  XP3 = 2,
  XP3s = 3,
  XPIRL = 4,
  XPIRL2 = 5,
  XPIRL3 = 6,
  XPIRL3_A = 7
};
extern enum SensorType sensor_type;
extern CyU3PEvent    glFxUVCEvent;
extern struct firmware_ctl_t firmware_ctrl_flag;
extern volatile CyBool_t IR_image_trigger;
/* Definitions to enable/disable special features in this UVC application. */
// Enable if Pan, Tilt and Zoom controls are to be implemented.
// #define UVC_PTZ_SUPPORT

// Enable if buffer overflow conditions are to be detected
// #define BACKFLOW_DETECT

// Enable UART debug prints to print the frame count every end of frame/
// #define DEBUG_PRINT_FRAME_COUNT

/* UVC application thread parameters. */
// Stack size for the video streaming thread is 4 KB.
#define UVC_APP_THREAD_STACK           (0x1000)
// Priority for the video streaming thread is 8.
#define UVC_APP_THREAD_PRIORITY        (8)
// Stack size for the UVC control request thread is 2 KB.
#define UVC_APP_EP0_THREAD_STACK       (0x0800)
// Priority for the UVC control request thread is 8.
#define UVC_APP_EP0_THREAD_PRIORITY    (8)
// Priority for the Data handle request thread is 10.
#define UVC_APP_DATA_THREAD_PRIORITY   (8)

/* DMA socket selection for UVC data transfer. */
// USB Consumer socket 3 is used for video data.
#define CY_FX_EP_VIDEO_CONS_SOCKET      0x03
// USB Consumer socket 2 is used for the status pipe.
#define CY_FX_EP_CONTROL_STATUS_SOCKET  0x02

/* Endpoint definition for UVC application */
// USB IN end points have MSB set
#define CY_FX_EP_IN_TYPE                0x80
// EP 3 IN
#define CY_FX_EP_BULK_VIDEO             (CY_FX_EP_VIDEO_CONS_SOCKET | CY_FX_EP_IN_TYPE)
// EP 2 IN
#define CY_FX_EP_CONTROL_STATUS         (CY_FX_EP_CONTROL_STATUS_SOCKET | CY_FX_EP_IN_TYPE)
// EP 2 OUT
#define CY_FX_EP_PRODUCER               0x04
// EP 2 IN
#define CY_FX_EP_CONSUMER               0x84
// EP 1 INTR
#define CY_FX_EP_INTERRUPT              0x81
#define CY_FX_EP_PRODUCER1_SOCKET        CY_U3P_UIB_SOCKET_PROD_4
#define CY_FX_EP_CONSUMER2_SOCKET        CY_U3P_UIB_SOCKET_CONS_4

/* UVC Video Streaming Endpoint Packet Size */
#define CY_FX_EP_BULK_VIDEO_PKT_SIZE    (0x400)         // 1024 Bytes

/* UVC Video Streaming Endpoint Packet Count */
#define CY_FX_EP_BULK_VIDEO_PKTS_COUNT  (0x10)          // 16 packets (burst of 16) per DMA buffer

/* DMA buffer size used for video streaming 16 KB  */
#define CY_FX_UVC_STREAM_BUF_SIZE    (CY_FX_EP_BULK_VIDEO_PKTS_COUNT * CY_FX_EP_BULK_VIDEO_PKT_SIZE)

/* Maximum video data that can be accommodated in one DMA buffer. */
#define CY_FX_UVC_BUF_FULL_SIZE         (CY_FX_UVC_STREAM_BUF_SIZE - 16)

/* Number of DMA buffers per GPIF DMA thread. */
#define CY_FX_UVC_STREAM_BUF_COUNT      (4)

/* Low Byte - UVC Video Streaming Endpoint Packet Size */
#define CY_FX_EP_BULK_VIDEO_PKT_SIZE_L  (uint8_t)(CY_FX_EP_BULK_VIDEO_PKT_SIZE & 0x00FF)

/* High Byte - UVC Video Streaming Endpoint Packet Size and No. of BULK packets */
#define CY_FX_EP_BULK_VIDEO_PKT_SIZE_H  (uint8_t)((CY_FX_EP_BULK_VIDEO_PKT_SIZE & 0xFF00) >> 8)

/* Event bits used for signaling the UVC application threads. */

/* Stream request event. Event flag that indicates that the streaming of video data has
   been enabled by the host. This flag is retained ON as long as video streaming is allowed,
   and is only turned off when the host indicates that data transfer should be stopped.
 */
#define CY_FX_UVC_STREAM_EVENT                  (1 << 0)

/* Abort streaming event. This event flag is set when the UVC host sends down a request
   (SET_INTERFACE or CLEAR_FEATURE) that indicates that video streaming should be stopped.
   The CY_FX_UVC_STREAM_EVENT event is cleared before setting this flag, and these two
   events can be considered as mutually exclusive.
 */
#define CY_FX_UVC_STREAM_ABORT_EVENT            (1 << 1)

/* UVC VIDEO_CONTROL_REQUEST event. This event flag indicates that a UVC class specific
   request addressed to the video control interface has been received. It should be cleared
   as soon as serviced by the firmware.
 */
#define CY_FX_UVC_VIDEO_CONTROL_REQUEST_EVENT   (1 << 2)

/* UVC VIDEO_STREAM_REQUEST event. This event flag indicates that a UVC class specific
   request addressed to the video streaming interface has been received. It should be cleared
   as soon as serviced by the firmware.
 */
#define CY_FX_UVC_VIDEO_STREAM_REQUEST_EVENT    (1 << 3)
/* GPIO Interrupt Event  */
#define CY_FX_UVC_GPIO0_INTR_CB_EVENT_FLAG      (1 << 4)
#define CY_FX_UVC_GPIO1_INTR_CB_EVENT_FLAG      (1 << 5)
#define CY_FX_UVC_DEBUG_INTR_CB_EVENT_FLAG      (1 << 6)

/*
   The following constants are taken from the USB and USB Video Class (UVC) specifications.
   They are defined here for convenient usage in the rest of the application source code.
 */
// Type code for Interface Association Descriptor (IAD)
#define CY_FX_INTF_ASSN_DSCR_TYPE       (0x0B)
// Mask for bmReqType field from a control request.
#define CY_FX_USB_SETUP_REQ_TYPE_MASK   (uint32_t)(0x000000FF)
// Mask for bRequest field from a control request.
#define CY_FX_USB_SETUP_REQ_MASK        (uint32_t)(0x0000FF00)
// Mask for wValue field from a control request.
#define CY_FX_USB_SETUP_VALUE_MASK      (uint32_t)(0xFFFF0000)
// Mask for wIndex field from a control request.
#define CY_FX_USB_SETUP_INDEX_MASK      (uint32_t)(0x0000FFFF)
// Mask for wLength field from a control request.
#define CY_FX_USB_SETUP_LENGTH_MASK     (uint32_t)(0xFFFF0000)
// USB SET_INTERFACE Request Type.
#define CY_FX_USB_SET_INTF_REQ_TYPE     (uint8_t)(0x01)
// USB SET_INTERFACE Request code.
#define CY_FX_USB_SET_INTERFACE_REQ     (uint8_t)(0x0B)
// Maximum UVC header size, in bytes.
#define CY_FX_UVC_MAX_HEADER           (12)
// Default BFH (Bit Field Header) for the UVC Header
#define CY_FX_UVC_HEADER_DEFAULT_BFH   (0x8C)
// Maximum number of bytes in Probe Control
#define CY_FX_UVC_MAX_PROBE_SETTING    (26)
// Probe control data size aligned to 16 bytes.
#define CY_FX_UVC_MAX_PROBE_SETTING_ALIGNED (32)
// UVC header value for normal frame indication
#define CY_FX_UVC_HEADER_FRAME          (0)
// UVC header value for end of frame indication
#define CY_FX_UVC_HEADER_EOF            (uint8_t)(1 << 1)
// Frame ID toggle bit in UVC header
#define CY_FX_UVC_HEADER_FRAME_ID       (uint8_t)(1 << 0)
// UVC Interface SET Request Type
#define CY_FX_USB_UVC_SET_REQ_TYPE      (uint8_t)(0x21)
// UVC Interface GET Request Type
#define CY_FX_USB_UVC_GET_REQ_TYPE      (uint8_t)(0xA1)
// UVC GET_CUR Request
#define CY_FX_USB_UVC_GET_CUR_REQ       (uint8_t)(0x81)
// UVC SET_CUR Request
#define CY_FX_USB_UVC_SET_CUR_REQ       (uint8_t)(0x01)
// UVC GET_MIN Request
#define CY_FX_USB_UVC_GET_MIN_REQ       (uint8_t)(0x82)
// UVC GET_MAX Request
#define CY_FX_USB_UVC_GET_MAX_REQ       (uint8_t)(0x83)
// UVC GET_RES Request
#define CY_FX_USB_UVC_GET_RES_REQ       (uint8_t)(0x84)
// UVC GET_LEN Request
#define CY_FX_USB_UVC_GET_LEN_REQ       (uint8_t)(0x85)
// UVC GET_INFO Request
#define CY_FX_USB_UVC_GET_INFO_REQ      (uint8_t)(0x86)
// UVC GET_DEF Request
#define CY_FX_USB_UVC_GET_DEF_REQ       (uint8_t)(0x87)
// Streaming Interface : Alternate Setting 1
#define CY_FX_UVC_STREAM_INTERFACE      (uint8_t)(1)
// Control Interface
#define CY_FX_UVC_CONTROL_INTERFACE     (uint8_t)(0)
// wValue setting used to access PROBE control.
#define CY_FX_UVC_PROBE_CTRL            (uint16_t)(0x0100)
// wValue setting used to access COMMIT control.
#define CY_FX_UVC_COMMIT_CTRL           (uint16_t)(0x0200)
// wIndex value used to select UVC interface control.
#define CY_FX_UVC_INTERFACE_CTRL        (uint8_t)(0)
// wIndex value used to select Camera terminal.
#define CY_FX_UVC_CAMERA_TERMINAL_ID    (uint8_t)(1)
// wIndex value used to select Processing Unit.
#define CY_FX_UVC_PROCESSING_UNIT_ID    (uint8_t)(2)
// wIndex value used to select Extension Unit.
#define CY_FX_UVC_EXTENSION_UNIT_ID     (uint8_t)(3)

#define VC_VIDEO_POWER_MODE_CONTROL     0x0100
#define VC_REQUEST_ERROR_CODE_CONTROL   0x0200
#define VC_SET_SEL_U1_U2_TEST           0x0000

// Processing Unit specific UVC control selector codes defined in the USB Video Class specification.
#define CY_FX_UVC_PU_BACKLIGHT_COMPENSATION_CONTROL         (uint16_t)(0x0100)
#define CY_FX_UVC_PU_BRIGHTNESS_CONTROL                     (uint16_t)(0x0200)
#define CY_FX_UVC_PU_CONTRAST_CONTROL                       (uint16_t)(0x0300)
#define CY_FX_UVC_PU_GAIN_CONTROL                           (uint16_t)(0x0400)
#define CY_FX_UVC_PU_POWER_LINE_FREQUENCY_CONTROL           (uint16_t)(0x0500)
#define CY_FX_UVC_PU_HUE_CONTROL                            (uint16_t)(0x0600)
#define CY_FX_UVC_PU_SATURATION_CONTROL                     (uint16_t)(0x0700)
#define CY_FX_UVC_PU_SHARPNESS_CONTROL                      (uint16_t)(0x0800)
#define CY_FX_UVC_PU_GAMMA_CONTROL                          (uint16_t)(0x0900)
#define CY_FX_UVC_PU_WHITE_BALANCE_TEMPERATURE_CONTROL      (uint16_t)(0x0A00)
#define CY_FX_UVC_PU_WHITE_BALANCE_TEMPERATURE_AUTO_CONTROL (uint16_t)(0x0B00)
#define CY_FX_UVC_PU_WHITE_BALANCE_COMPONENT_CONTROL        (uint16_t)(0x0C00)
#define CY_FX_UVC_PU_WHITE_BALANCE_COMPONENT_AUTO_CONTROL   (uint16_t)(0x0D00)
#define CY_FX_UVC_PU_DIGITAL_MULTIPLIER_CONTROL             (uint16_t)(0x0E00)
#define CY_FX_UVC_PU_DIGITAL_MULTIPLIER_LIMIT_CONTROL       (uint16_t)(0x0F00)
#define CY_FX_UVC_PU_HUE_AUTO_CONTROL                       (uint16_t)(0x1000)
#define CY_FX_UVC_PU_ANALOG_VIDEO_STANDARD_CONTROL          (uint16_t)(0x1100)
#define CY_FX_UVC_PU_ANALOG_LOCK_STATUS_CONTROL             (uint16_t)(0x1200)

// Camera Terminal specific UVC control selector codes defined in the USB Video Class specification.
#define CY_FX_UVC_CT_SCANNING_MODE_CONTROL                  (uint16_t)(0x0100)
#define CY_FX_UVC_CT_AE_MODE_CONTROL                        (uint16_t)(0x0200)
#define CY_FX_UVC_CT_AE_PRIORITY_CONTROL                    (uint16_t)(0x0300)
#define CY_FX_UVC_CT_EXPOSURE_TIME_ABSOLUTE_CONTROL         (uint16_t)(0x0400)
#define CY_FX_UVC_CT_EXPOSURE_TIME_RELATIVE_CONTROL         (uint16_t)(0x0500)
#define CY_FX_UVC_CT_FOCUS_ABSOLUTE_CONTROL                 (uint16_t)(0x0600)
#define CY_FX_UVC_CT_FOCUS_RELATIVE_CONTROL                 (uint16_t)(0x0700)
#define CY_FX_UVC_CT_FOCUS_AUTO_CONTROL                     (uint16_t)(0x0800)
#define CY_FX_UVC_CT_IRIS_ABSOLUTE_CONTROL                  (uint16_t)(0x0900)
#define CY_FX_UVC_CT_IRIS_RELATIVE_CONTROL                  (uint16_t)(0x0A00)
#define CY_FX_UVC_CT_ZOOM_ABSOLUTE_CONTROL                  (uint16_t)(0x0B00)
#define CY_FX_UVC_CT_ZOOM_RELATIVE_CONTROL                  (uint16_t)(0x0C00)
#define CY_FX_UVC_CT_PANTILT_ABSOLUTE_CONTROL               (uint16_t)(0x0D00)
#define CY_FX_UVC_CT_PANTILT_RELATIVE_CONTROL               (uint16_t)(0x0E00)
#define CY_FX_UVC_CT_ROLL_ABSOLUTE_CONTROL                  (uint16_t)(0x0F00)
#define CY_FX_UVC_CT_ROLL_RELATIVE_CONTROL                  (uint16_t)(0x1000)
#define CY_FX_UVC_CT_PRIVACY_CONTROL                        (uint16_t)(0x1100)

// extention unit control selector
#define CY_FX_UVC_XU_SPI_FLASH                              (uint16_t)(0x0a00)
#define CY_FX_UVC_XU_CAM_REG                                (uint16_t)(0x0b00)
#define CY_FX_UVC_XU_REG_BURST                              (uint16_t)(0x0c00)
#define CY_FX_UVC_XU_SVER_RW                                (uint16_t)(0x0d00)
#define CY_FX_UVC_XU_REG_RW                                 (uint16_t)(0x0e00)
#define CY_FX_UVC_XU_HVER_RW                                (uint16_t)(0x0f00)
#define CY_FX_UVC_XU_FLAG_RW                                (uint16_t)(0x1000)
#define CY_FX_UVC_XU_IR_RW                                  (uint16_t)(0x1100)
#define CY_FX_UVC_XU_SPLAH_RW                               (uint16_t)(0x1200)
#define CY_FX_UVC_XU_DEBUG_RW                               (uint16_t)(0x1300)
#define CY_FX_UVC_XU_CALIB_RW                               (uint16_t)(0x1400)

extern void CyFxAppErrorHandler(CyU3PReturnStatus_t apiRetStatus);
#endif  // FIRMWARE_INCLUDE_UVC_H_
